U60NMTMiner/Arduino-Python_sensor_datalink/Example Data/2024-02-22_20-28_data.xlsx Data and Commentary/20240222_210228.jpg

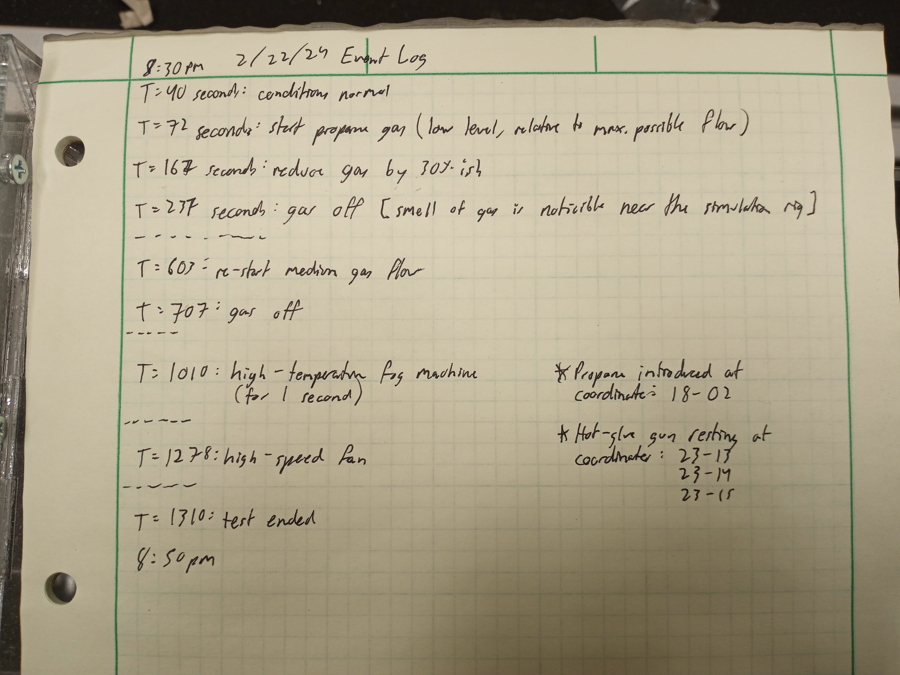
Example Data/2024-02-22_20-28_data.xlsx Data and Commentary/20240222_210228.jpg
