U60NMTMiner/Arduino-Python_sensor_datalink/Example Data/2024-02-26_18-05_data.xlsx Data and Commentary/20240226_185721.jpg

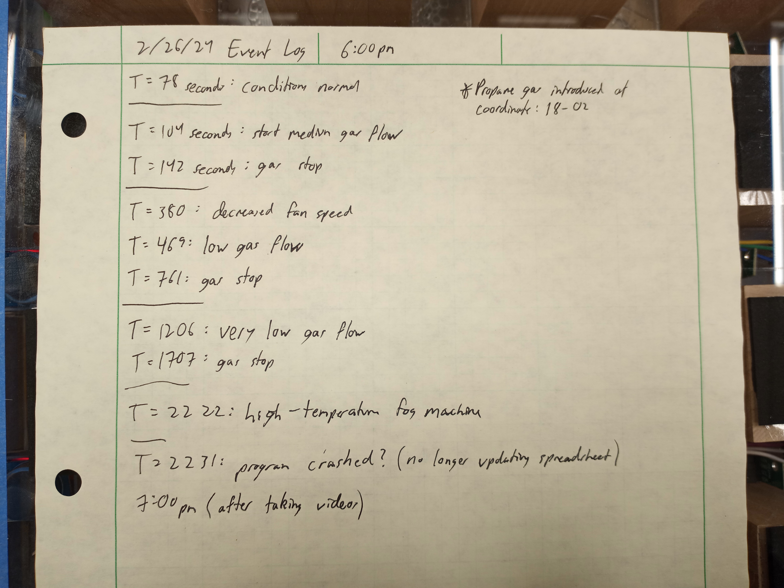
Example Data/2024-02-26_18-05_data.xlsx Data and Commentary/20240226_185721.jpg
